Tinkerforge/thermal-imaging-bricklet/software/src/lepton.c

/* thermal-imaging-bricklet
 * Copyright (C) 2017 Olaf Lüke <olaf@tinkerforge.com>
 *
 * lepton.c: Lepton thermal imaging camera module communication
 *
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
 * You should have received a copy of the GNU Lesser General Public
 * License along with this library; if not, write to the
 * Free Software Foundation, Inc., 59 Temple Place - Suite 330,
 * Boston, MA 02111-1307, USA.
 */

#include "lepton.h"

#include <stdbool.h>

#include "configs/config.h"
#include "configs/config_lepton.h"

#include "bricklib2/hal/system_timer/system_timer.h"
#include "bricklib2/utility/crc16.h"

#include "communication.h"

#include "xmc_i2c.h"
#include "xmc_spi.h"
#include "xmc_gpio.h"
#include "xmc_usic.h"
#include "xmc_eru.h"

#define lepton_rx_read_irq_handler   IRQ_Hdlr_11
#define lepton_rx_remove_irq_handler IRQ_Hdlr_12
#define lepton_sync_handler          IRQ_Hdlr_3

extern Lepton lepton;

uint16_t * const lepton_frame_start = lepton.frame.buffer;
uint16_t * const lepton_frame_end = lepton.frame.buffer + LEPTON_FRAME_SIZE_WITH_TELEMETRY;
uint16_t * const lepton_frame_end_of_first_packet = lepton.frame.buffer + LEPTON_PACKET_SIZE;
uint16_t * const lepton_frame_last_full = lepton.frame.buffer + LEPTON_FRAME_SIZE_WITH_TELEMETRY-12;
uint16_t * const lepton_frame_first_packet_last_full = lepton.frame.buffer + LEPTON_PACKET_SIZE-2;
uint16_t *lepton_frame_pointer = lepton.frame.buffer;
uint16_t *lepton_frame_pointer_dummy = lepton.frame.buffer;

#if 0
uint16_t * const lepton_packet_start = lepton.packet.buffer;
uint16_t * const lepton_packet_end = lepton.packet.buffer + LEPTON_PACKET_SIZE;
uint16_t * const lepton_packet_last_full = lepton.packet.buffer + LEPTON_PACKET_SIZE-2;
uint16_t *lepton_packet_pointer = lepton.packet.buffer;
#endif

#define LEPTON_SET_SPI_LIMIT(limit) do {\
	LEPTON_SPI->RBCTR = (uint32_t)((LEPTON_SPI->RBCTR & (uint32_t)~USIC_CH_RBCTR_LIMIT_Msk) | ((limit) << USIC_CH_RBCTR_LIMIT_Pos));\
} while(0)

#define LEPTON_SPI_WRITE_1() do {\
	LEPTON_SPI_IN_PTR[0] = 0;\
} while(0)


#define LEPTON_SPI_WRITE_2() do {\
	LEPTON_SPI_WRITE_1();\
	LEPTON_SPI_WRITE_1();\
} while(0)

#define LEPTON_SPI_WRITE_4() do {\
	LEPTON_SPI_WRITE_2();\
	LEPTON_SPI_WRITE_2();\
} while(0)

#define LEPTON_SPI_WRITE_6() do {\
	LEPTON_SPI_WRITE_4();\
	LEPTON_SPI_WRITE_2();\
} while(0)

#define LEPTON_SPI_WRITE_8() do {\
	LEPTON_SPI_WRITE_6();\
	LEPTON_SPI_WRITE_2();\
} while(0)

#define LEPTON_SPI_WRITE_10() do {\
	LEPTON_SPI_WRITE_8();\
	LEPTON_SPI_WRITE_2();\
} while(0)

#define LEPTON_SPI_WRITE_12() do {\
	LEPTON_SPI_WRITE_10();\
	LEPTON_SPI_WRITE_2();\
} while(0)

#define LEPTON_SPI_WRITE_14() do {\
	LEPTON_SPI_WRITE_12();\
	LEPTON_SPI_WRITE_2();\
} while(0)

#define LEPTON_SPI_WRITE_16() do {\
	LEPTON_SPI_WRITE_14();\
	LEPTON_SPI_WRITE_2();\
} while(0)

#define LEPTON_SPI_READ_1() do {\
	*lepton_frame_pointer++ = *LEPTON_SPI_OUTR_PTR;\
} while(0)

#define LEPTON_SPI_READ_2() do {\
	LEPTON_SPI_READ_1();\
	LEPTON_SPI_READ_1();\
} while(0)

#define LEPTON_SPI_READ_4() do {\
	LEPTON_SPI_READ_2();\
	LEPTON_SPI_READ_2();\
} while(0)

#define LEPTON_SPI_READ_6() do {\
	LEPTON_SPI_READ_4();\
	LEPTON_SPI_READ_2();\
} while(0)

#define LEPTON_SPI_READ_8() do {\
	LEPTON_SPI_READ_6();\
	LEPTON_SPI_READ_2();\
} while(0)

#define LEPTON_SPI_READ_10() do {\
	LEPTON_SPI_READ_8();\
	LEPTON_SPI_READ_2();\
} while(0)

#define LEPTON_SPI_READ_12() do {\
	LEPTON_SPI_READ_10();\
	LEPTON_SPI_READ_2();\
} while(0)

#define LEPTON_SPI_READ_14() do {\
	LEPTON_SPI_READ_12();\
	LEPTON_SPI_READ_2();\
} while(0)

#define LEPTON_SPI_READ_16() do {\
	LEPTON_SPI_READ_14();\
	LEPTON_SPI_READ_2();\
} while(0)

#define LEPTON_SPI_REMOVE_1() do {\
	*LEPTON_SPI_OUTR_PTR;\
	lepton_frame_pointer_dummy++;\
} while(0)

#define LEPTON_SPI_REMOVE_2() do {\
	LEPTON_SPI_REMOVE_1();\
	LEPTON_SPI_REMOVE_1();\
} while(0)

#define LEPTON_SPI_REMOVE_4() do {\
	LEPTON_SPI_REMOVE_2();\
	LEPTON_SPI_REMOVE_2();\
} while(0)

#define LEPTON_SPI_REMOVE_6() do {\
	LEPTON_SPI_REMOVE_4();\
	LEPTON_SPI_REMOVE_2();\
} while(0)

#define LEPTON_SPI_REMOVE_8() do {\
	LEPTON_SPI_REMOVE_6();\
	LEPTON_SPI_REMOVE_2();\
} while(0)

#define LEPTON_SPI_REMOVE_10() do {\
	LEPTON_SPI_REMOVE_8();\
	LEPTON_SPI_REMOVE_2();\
} while(0)

#define LEPTON_SPI_REMOVE_12() do {\
	LEPTON_SPI_REMOVE_10();\
	LEPTON_SPI_REMOVE_2();\
} while(0)

#define LEPTON_SPI_REMOVE_14() do {\
	LEPTON_SPI_REMOVE_12();\
	LEPTON_SPI_REMOVE_2();\
} while(0)

#define LEPTON_SPI_REMOVE_16() do {\
	LEPTON_SPI_REMOVE_14();\
	LEPTON_SPI_REMOVE_2();\
} while(0)

typedef enum {
	LEPTON_IRQ_STATE_SYNC,
	LEPTON_IRQ_STATE_DATA
} LeptonIRQState;

static LeptonIRQState lepton_irq_state = LEPTON_IRQ_STATE_SYNC;

void __attribute__((optimize("-O3"))) lepton_sync_handler(void) {
	if(!lepton.sync_done || lepton.active_interface != LEPTON_INTERFACE_SPI || !XMC_GPIO_GetInput(LEPTON_SELECT_PIN)) {
		return;
	}

	// Use local pointer to save the time for accessing the struct
	volatile const uint32_t *LEPTON_SPI_OUTR_PTR = &LEPTON_SPI->OUTR;
	volatile uint32_t       *LEPTON_SPI_IN_PTR   =  LEPTON_SPI->IN;

	// Make sure SPI FIFO is flushed
	for(uint8_t i = 0; i < 32; i++) {
		*LEPTON_SPI_OUTR_PTR;
	}

	if(lepton.state == LEPTON_STATE_READ_FRAME) {
		XMC_USIC_CH_RXFIFO_SetInterruptNodePointer(LEPTON_SPI, XMC_USIC_CH_RXFIFO_INTERRUPT_NODE_POINTER_STANDARD, LEPTON_SERVICE_REQUEST_READ_RX);   // IRQ LEPTON_IRQ_READ_RX
		NVIC_DisableIRQ((IRQn_Type)LEPTON_IRQ_REMOVE_RX);
		NVIC_EnableIRQ((IRQn_Type)LEPTON_IRQ_READ_RX);
		lepton_frame_pointer = lepton_frame_start;
	} else {
		XMC_USIC_CH_RXFIFO_SetInterruptNodePointer(LEPTON_SPI, XMC_USIC_CH_RXFIFO_INTERRUPT_NODE_POINTER_STANDARD, LEPTON_SERVICE_REQUEST_REMOVE_RX); // IRQ LEPTON_IRQ_REMOVE_RX
		NVIC_DisableIRQ((IRQn_Type)LEPTON_IRQ_READ_RX);
		NVIC_EnableIRQ((IRQn_Type)LEPTON_IRQ_REMOVE_RX);
		lepton_frame_pointer_dummy = lepton_frame_start;
	}
	XMC_GPIO_SetOutputLow(LEPTON_SELECT_PIN);

	LEPTON_SET_SPI_LIMIT(15);
	lepton_irq_state = LEPTON_IRQ_STATE_SYNC;
	LEPTON_SPI_WRITE_16();
}

void __attribute__((optimize("-O3"))) __attribute__ ((section (".ram_code"))) lepton_rx_read_irq_handler(void) {
	// Use local pointer to save the time for accessing the struct
	volatile const uint32_t *LEPTON_SPI_OUTR_PTR = &LEPTON_SPI->OUTR;
	volatile uint32_t       *LEPTON_SPI_IN_PTR   =  LEPTON_SPI->IN;

	if(lepton_irq_state == LEPTON_IRQ_STATE_SYNC) {
		LEPTON_SPI_READ_2();
		if(lepton_frame_pointer != lepton_frame_end_of_first_packet) {
			LEPTON_SPI_READ_14();
			LEPTON_SPI_WRITE_2();
			if(lepton_frame_pointer != lepton_frame_first_packet_last_full) {
				LEPTON_SPI_WRITE_14();
			} else {
				LEPTON_SET_SPI_LIMIT(1);
			}
		} else {
			if((lepton.frame.data.packets[0].vospi.id & LEPTON_SPI_PACKET_ID_MASK) != 0) {
				lepton_frame_pointer = lepton_frame_start;
			} else {
				lepton_irq_state = LEPTON_IRQ_STATE_DATA;
			}
			LEPTON_SET_SPI_LIMIT(15);
			LEPTON_SPI_WRITE_16();
		}
	} else {
		LEPTON_SPI_READ_12();
		if(lepton_frame_pointer != lepton_frame_end) {
			// Write 10 words already before we read the next 4, we can save some waiting time between packets with this.
			// We don't write the full 12 bytes, we may get an early interrupt if we do.
			LEPTON_SPI_WRITE_10();
			LEPTON_SPI_READ_4();
			LEPTON_SPI_WRITE_2();
			if(lepton_frame_pointer != lepton_frame_last_full) {
				LEPTON_SPI_WRITE_4();
			} else {
				LEPTON_SET_SPI_LIMIT(11);
			}
		} else {
			lepton.state = LEPTON_STATE_CHECK_CRC;
			lepton.config_handle_now = true;
			XMC_GPIO_SetOutputHigh(LEPTON_SELECT_PIN);
		}
	}
}

void __attribute__((optimize("-O3"))) __attribute__ ((section (".ram_code"))) lepton_rx_remove_irq_handler(void) {
	// Use local pointer to save the time for accessing the struct
	volatile const uint32_t *LEPTON_SPI_OUTR_PTR = &LEPTON_SPI->OUTR;
	volatile uint32_t       *LEPTON_SPI_IN_PTR   =  LEPTON_SPI->IN;

	if(lepton_irq_state == LEPTON_IRQ_STATE_SYNC) {
		LEPTON_SPI_REMOVE_2();
		if(lepton_frame_pointer_dummy != lepton_frame_end_of_first_packet) {
			LEPTON_SPI_REMOVE_14();
			LEPTON_SPI_WRITE_2();
			if(lepton_frame_pointer_dummy != lepton_frame_first_packet_last_full) {
				LEPTON_SPI_WRITE_14();
			} else {
				LEPTON_SET_SPI_LIMIT(1);
			}
		} else {
			if((lepton.frame.data.packets[0].vospi.id & LEPTON_SPI_PACKET_ID_MASK) != 0) {
				lepton_frame_pointer_dummy = lepton_frame_start;
			} else {
				lepton_irq_state = LEPTON_IRQ_STATE_DATA;
			}
			LEPTON_SET_SPI_LIMIT(15);
			LEPTON_SPI_WRITE_16();
		}
	} else {
		LEPTON_SPI_REMOVE_12();
		if(lepton_frame_pointer_dummy != lepton_frame_end) {
			// Write 10 words already before we read the next 4, we can save some waiting time between packets with this.
			// We don't write the full 12 bytes, we may get an early interrupt if we do.
			LEPTON_SPI_WRITE_10();
			LEPTON_SPI_REMOVE_4();
			LEPTON_SPI_WRITE_2();
			if(lepton_frame_pointer_dummy != lepton_frame_last_full) {
				LEPTON_SPI_WRITE_4();
			} else {
				LEPTON_SET_SPI_LIMIT(11);
			}
		} else {
			XMC_GPIO_SetOutputHigh(LEPTON_SELECT_PIN);
			lepton.config_handle_now = true;
		}
	}
}

void lepton_i2c_write(Lepton *lepton, const uint16_t reg, const uint16_t length, const uint16_t *data, bool send_stop) {
	// Send address
	XMC_I2C_CH_MasterStart(LEPTON_I2C, LEPTON_I2C_ADDRESS << 1, XMC_I2C_CH_CMD_WRITE);

	// Wait for ACK
	while(!(XMC_I2C_CH_GetStatusFlag(LEPTON_I2C) & XMC_I2C_CH_STATUS_FLAG_ACK_RECEIVED));
	XMC_I2C_CH_ClearStatusFlag(LEPTON_I2C, XMC_I2C_CH_STATUS_FLAG_ACK_RECEIVED);

	// Transmit 16 bit register
	XMC_I2C_CH_MasterTransmit(LEPTON_I2C, reg >> 8);
	XMC_I2C_CH_MasterTransmit(LEPTON_I2C, reg & 0xFF);

	// Transmit data
	uint32_t index = 0;
	bool high = true;
	while(index < length) {
		while(!XMC_USIC_CH_TXFIFO_IsFull(LEPTON_I2C)) {
			if(index < length) {
				if(high) {
					// Send high byte first
					XMC_I2C_CH_MasterTransmit(LEPTON_I2C, data[index] >> 8);
					high = false;
				} else {
					// and low byte second
					XMC_I2C_CH_MasterTransmit(LEPTON_I2C, data[index] & 0xFF);
					high = true;
					index++;
				}
			} else {
				break;
			}
		}
	}

	// Wait for data to be written
	while(!XMC_USIC_CH_TXFIFO_IsEmpty(LEPTON_I2C));

	if(send_stop) {
		// Send stop
		XMC_I2C_CH_MasterStop(LEPTON_I2C);
	}
}

void lepton_i2c_read(Lepton *lepton, const uint16_t reg, const uint32_t length, uint16_t *data) {
	// Write register address to read from without stop bit
	lepton_i2c_write(lepton, reg, 0, NULL, false);

	// Repeated start
	XMC_I2C_CH_MasterRepeatedStart(LEPTON_I2C, LEPTON_I2C_ADDRESS << 1, XMC_I2C_CH_CMD_READ);

	// Wait for ACK
	while(!(XMC_I2C_CH_GetStatusFlag(LEPTON_I2C) & XMC_I2C_CH_STATUS_FLAG_ACK_RECEIVED));
	XMC_I2C_CH_ClearStatusFlag(LEPTON_I2C, XMC_I2C_CH_STATUS_FLAG_ACK_RECEIVED);

	uint32_t fifo_index = 0;
	uint32_t data_index = 0;
	bool high = true;
	while(fifo_index < length*2) {
		while(!XMC_USIC_CH_TXFIFO_IsFull(LEPTON_I2C)) {
			if(fifo_index < length*2) {
				if(fifo_index+1 == length*2) {
					XMC_I2C_CH_MasterReceiveNack(LEPTON_I2C);
				} else {
					XMC_I2C_CH_MasterReceiveAck(LEPTON_I2C);
				}
				fifo_index++;
			} else {
				break;
			}
		}

		while(data_index < fifo_index) {
			while(XMC_USIC_CH_RXFIFO_IsEmpty(LEPTON_I2C));
			if(high) {
				// Get high byte first
				data[data_index/2] = XMC_I2C_CH_GetReceivedData(LEPTON_I2C) << 8;
				high = false;
			} else {
				// and low byte second
				data[data_index/2] |= XMC_I2C_CH_GetReceivedData(LEPTON_I2C);
				high = true;
			}
			data_index++;
		}
	}
	XMC_I2C_CH_MasterStop(LEPTON_I2C);
}

void lepton_spi_select(Lepton *lepton) {
	XMC_GPIO_SetOutputLow(LEPTON_SELECT_PIN);
}

void lepton_spi_deselect(Lepton *lepton) {
	XMC_GPIO_SetOutputHigh(LEPTON_SELECT_PIN);
}

uint16_t lepton_get_status(Lepton *lepton) {
	uint16_t status = 0;
	lepton_i2c_read(lepton, LEPTON_I2C_STATUS_REG, 1, &status);
	return status;
}

bool lepton_is_busy(Lepton *lepton) {
	uint16_t status = lepton_get_status(lepton);
	return status & LEPTON_I2C_STATUS_BUSY_BITMASK;
}

void lepton_command_run(Lepton *lepton, const uint16_t command_id) {
	while(lepton_is_busy(lepton));

	// Write command
	uint16_t command = command_id | LEPTON_I2C_COMMAND_TYPE_RUN;
	lepton_i2c_write(lepton, LEPTON_I2C_COMMAND_REG, 1, &command, true);

	while(lepton_is_busy(lepton));
}

void lepton_attribute_read(Lepton *lepton, const uint16_t command_id, const uint16_t length, uint16_t *data) {
	while(lepton_is_busy(lepton));

	// Write length to be read
	lepton_i2c_write(lepton, LEPTON_I2C_DATA_LENGTH_REG, 1, &length, true);

	// Write command
	uint16_t command = command_id | LEPTON_I2C_COMMAND_TYPE_GET;
	lepton_i2c_write(lepton, LEPTON_I2C_COMMAND_REG, 1, &command, true);

	while(lepton_is_busy(lepton));

	// Read data
	lepton_i2c_read(lepton, LEPTON_I2C_DATA_0_REG, length, data);
}

void lepton_attribute_write(Lepton *lepton, const uint16_t command_id, const uint16_t length, uint16_t *data) {
	while(lepton_is_busy(lepton));

	// Write data (we assume length <= 16 here)
	lepton_i2c_write(lepton, LEPTON_I2C_DATA_0_REG, length, data, true);

	// Write length
	lepton_i2c_write(lepton, LEPTON_I2C_DATA_LENGTH_REG, 1, &length, true);

	// Write command
	uint16_t command = command_id | LEPTON_I2C_COMMAND_TYPE_SET;
	lepton_i2c_write(lepton, LEPTON_I2C_COMMAND_REG, 1, &command, true);

	while(lepton_is_busy(lepton));
}

void lepton_reset(Lepton *lepton) {
	XMC_GPIO_SetOutputLow(LEPTON_NRESET_PIN);
	lepton->reset_start_time = system_timer_get_ms();
	lepton->state = LEPTON_STATE_RESET;
}

void lepton_init_spi(Lepton *lepton) {
	if(lepton->active_interface == LEPTON_INTERFACE_SPI) {
		return;
	}

	// -- First disable I2C --
	XMC_I2C_CH_Stop(LEPTON_I2C);

	const XMC_GPIO_CONFIG_t sda_pin_config =  {
		.mode         = XMC_GPIO_MODE_INPUT_TRISTATE,
		.output_level = XMC_GPIO_OUTPUT_LEVEL_HIGH,
	};

	const XMC_GPIO_CONFIG_t scl_pin_config = {
		.mode         = XMC_GPIO_MODE_INPUT_TRISTATE,
		.output_level = XMC_GPIO_OUTPUT_LEVEL_HIGH,
	};

	XMC_GPIO_Init(LEPTON_SDA_PIN, &sda_pin_config);
	XMC_GPIO_Init(LEPTON_SCL_PIN, &scl_pin_config);


	// -- Then enable SPI --

	// USIC channel configuration
	const XMC_SPI_CH_CONFIG_t channel_config = {
		.baudrate       = LEPTON_SPI_BAUDRATE,
		.bus_mode       = XMC_SPI_CH_BUS_MODE_MASTER,
		.selo_inversion = XMC_SPI_CH_SLAVE_SEL_INV_TO_MSLS,
		.parity_mode    = XMC_USIC_CH_PARITY_MODE_NONE
	};

	// MISO pin configuration
	const XMC_GPIO_CONFIG_t miso_pin_config = {
		.mode             = XMC_GPIO_MODE_INPUT_TRISTATE,
		.input_hysteresis = XMC_GPIO_INPUT_HYSTERESIS_LARGE
	};

	// SCLK pin configuration
	const XMC_GPIO_CONFIG_t sclk_pin_config = {
		.mode             = LEPTON_SCLK_PIN_AF,
		.output_level     = XMC_GPIO_OUTPUT_LEVEL_HIGH
	};

	// SELECT pin configuration
	const XMC_GPIO_CONFIG_t select_pin_config = {
		.mode             = XMC_GPIO_MODE_OUTPUT_PUSH_PULL, // we set cs high/low by hand
		.output_level     = XMC_GPIO_OUTPUT_LEVEL_HIGH
	};

	// Configure MISO pin
	XMC_GPIO_Init(LEPTON_MISO_PIN, &miso_pin_config);

	// Initialize USIC channel in SPI master mode
	XMC_SPI_CH_Init(LEPTON_SPI, &channel_config);
	LEPTON_SPI->SCTR &= ~USIC_CH_SCTR_PDL_Msk; // Set passive data level to 0
	LEPTON_SPI->PCR_SSCMode &= ~USIC_CH_PCR_SSCMode_TIWEN_Msk; // Disable time between bytes

	XMC_SPI_CH_SetBitOrderMsbFirst(LEPTON_SPI);

	XMC_SPI_CH_SetWordLength(LEPTON_SPI, 16);
	XMC_SPI_CH_SetFrameLength(LEPTON_SPI, 64);

	XMC_SPI_CH_SetTransmitMode(LEPTON_SPI, XMC_SPI_CH_MODE_STANDARD);

	// Configure the clock polarity and clock delay
	XMC_SPI_CH_ConfigureShiftClockOutput(LEPTON_SPI,
									     XMC_SPI_CH_BRG_SHIFT_CLOCK_PASSIVE_LEVEL_1_DELAY_DISABLED,
									     XMC_SPI_CH_BRG_SHIFT_CLOCK_OUTPUT_SCLK);
	// Configure Leading/Trailing delay
	XMC_SPI_CH_SetSlaveSelectDelay(LEPTON_SPI, 2);

	// Set input source path
	XMC_SPI_CH_SetInputSource(LEPTON_SPI, LEPTON_MISO_INPUT, LEPTON_MISO_SOURCE);

	// SPI Mode: CPOL=1 and CPHA=1
	LEPTON_SPI_CHANNEL->DX1CR |= USIC_CH_DX1CR_DPOL_Msk;

	XMC_USIC_CH_TXFIFO_Flush(LEPTON_SPI);
	XMC_USIC_CH_RXFIFO_Flush(LEPTON_SPI);

	// Configure transmit FIFO
	XMC_USIC_CH_TXFIFO_Configure(LEPTON_SPI, 48, XMC_USIC_CH_FIFO_SIZE_16WORDS, 0);

	// Configure receive FIFO
	XMC_USIC_CH_RXFIFO_Configure(LEPTON_SPI, 32, XMC_USIC_CH_FIFO_SIZE_16WORDS, 15);

	// Set priority and enable NVIC node for receive interrupt
	NVIC_SetPriority((IRQn_Type)LEPTON_IRQ_READ_RX, LEPTON_IRQ_RX_PRIORITY);
	NVIC_SetPriority((IRQn_Type)LEPTON_IRQ_REMOVE_RX, LEPTON_IRQ_RX_PRIORITY);

	// Start SPI
	XMC_SPI_CH_Start(LEPTON_SPI);

	// Configure SCLK pin
	XMC_GPIO_Init(LEPTON_SCLK_PIN, &sclk_pin_config);

	// Configure slave select pin
	XMC_GPIO_Init(LEPTON_SELECT_PIN, &select_pin_config);

	XMC_USIC_CH_RXFIFO_EnableEvent(LEPTON_SPI, XMC_USIC_CH_RXFIFO_EVENT_CONF_STANDARD | XMC_USIC_CH_RXFIFO_EVENT_CONF_ALTERNATE);

	lepton->active_interface = LEPTON_INTERFACE_SPI;
}

void lepton_init_i2c(Lepton *lepton) {
	if(lepton->active_interface == LEPTON_INTERFACE_I2C) {
		return;
	}

	// -- First disable SPI --

	XMC_SPI_CH_Stop(LEPTON_SPI);
	lepton_spi_deselect(lepton);

	NVIC_DisableIRQ((IRQn_Type)LEPTON_IRQ_REMOVE_RX);
	NVIC_DisableIRQ((IRQn_Type)LEPTON_IRQ_READ_RX);

	XMC_USIC_CH_RXFIFO_DisableEvent(LEPTON_SPI, XMC_USIC_CH_RXFIFO_EVENT_CONF_STANDARD | XMC_USIC_CH_RXFIFO_EVENT_CONF_ALTERNATE);

	// MISO pin configuration
	const XMC_GPIO_CONFIG_t miso_pin_config = {
		.mode             = XMC_GPIO_MODE_INPUT_TRISTATE,
		.input_hysteresis = XMC_GPIO_INPUT_HYSTERESIS_LARGE
	};

	// SCLK pin configuration
	const XMC_GPIO_CONFIG_t sclk_pin_config = {
		.mode             = XMC_GPIO_MODE_OUTPUT_PUSH_PULL,
		.output_level     = XMC_GPIO_OUTPUT_LEVEL_HIGH
	};

	// SELECT pin configuration
	const XMC_GPIO_CONFIG_t select_pin_config = {
		.mode             = XMC_GPIO_MODE_OUTPUT_PUSH_PULL,
		.output_level     = XMC_GPIO_OUTPUT_LEVEL_HIGH
	};

	XMC_GPIO_Init(LEPTON_SCLK_PIN, &sclk_pin_config);
	XMC_GPIO_Init(LEPTON_MISO_PIN, &miso_pin_config);
	XMC_GPIO_Init(LEPTON_SELECT_PIN, &select_pin_config);

	LEPTON_SPI->SCTR |= USIC_CH_SCTR_PDL_Msk; // Set passive data level to 1
	LEPTON_SPI_CHANNEL->DX1CR &= ~USIC_CH_DX1CR_DPOL_Msk; // Set input control register back to default


	// -- Then enable I2C --

	const XMC_I2C_CH_CONFIG_t master_channel_config = {
		.baudrate = LEPTON_I2C_BAUDRATE,
		.address  = 0
	};

	const XMC_GPIO_CONFIG_t sda_pin_config =  {
		.mode         = LEPTON_SDA_PIN_MODE,
		.output_level = XMC_GPIO_OUTPUT_LEVEL_HIGH,
	};

	const XMC_GPIO_CONFIG_t scl_pin_config = {
		.mode         = LEPTON_SCL_PIN_MODE,
		.output_level = XMC_GPIO_OUTPUT_LEVEL_HIGH,
	};

	XMC_I2C_CH_Init(LEPTON_I2C, &master_channel_config);

	XMC_USIC_CH_SetInputSource(LEPTON_I2C, LEPTON_SDA_INPUT, LEPTON_SDA_SOURCE);
	XMC_USIC_CH_SetInputSource(LEPTON_I2C, LEPTON_SCL_INPUT, LEPTON_SCL_SOURCE);

	XMC_USIC_CH_TXFIFO_Flush(LEPTON_I2C);
	XMC_USIC_CH_RXFIFO_Flush(LEPTON_I2C);

	XMC_USIC_CH_TXFIFO_Configure(LEPTON_I2C, 48, XMC_USIC_CH_FIFO_SIZE_16WORDS, 0);
	XMC_USIC_CH_RXFIFO_Configure(LEPTON_I2C, 32, XMC_USIC_CH_FIFO_SIZE_16WORDS, 0);

	XMC_I2C_CH_Start(LEPTON_I2C);

	XMC_GPIO_Init(LEPTON_SDA_PIN, &sda_pin_config);
	XMC_GPIO_Init(LEPTON_SCL_PIN, &scl_pin_config);

	lepton->active_interface = LEPTON_INTERFACE_I2C;
}

void lepton_init_gpio(Lepton *lepton) {
	const XMC_GPIO_CONFIG_t nreset_pin_config = {
		.mode         = XMC_GPIO_MODE_OUTPUT_PUSH_PULL,
		.output_level = XMC_GPIO_OUTPUT_LEVEL_LOW,
	};
	XMC_GPIO_Init(LEPTON_NRESET_PIN, &nreset_pin_config);

	const XMC_GPIO_CONFIG_t sync_pin_config = {
		.mode             = XMC_GPIO_MODE_INPUT_TRISTATE,
		.input_hysteresis = XMC_GPIO_INPUT_HYSTERESIS_LARGE
	};
	XMC_GPIO_Init(P0_0, &sync_pin_config); // TODO: Remove me for release version

	const XMC_ERU_ETL_CONFIG_t sync_etl_config = {
		.input_a                = (uint32_t)XMC_ERU_ETL_INPUT_A0,
		.input_b                = (uint32_t)XMC_ERU_ETL_INPUT_B0,
		.enable_output_trigger  = (uint32_t)1,
		.edge_detection         = XMC_ERU_ETL_EDGE_DETECTION_RISING,
		.output_trigger_channel = XMC_ERU_ETL_OUTPUT_TRIGGER_CHANNEL0, // Select the source for event
		.source                 = XMC_ERU_ETL_SOURCE_B
	};

	// Initializes input pin characteristics
	XMC_GPIO_Init(LEPTON_SYNC_PIN, &sync_pin_config);
	// ERU Event Trigger Logic Hardware initialization based on UI
	XMC_ERU_ETL_Init(XMC_ERU0, LEPTON_SYNC_ETL_CHANNEL, &sync_etl_config);
	// OGU is configured to generate event on configured trigger edge
	XMC_ERU_OGU_SetServiceRequestMode(XMC_ERU0, LEPTON_SYNC_OGU_CHANNEL, XMC_ERU_OGU_SERVICE_REQUEST_ON_TRIGGER);
	// Configure NVIC node and priority
	NVIC_SetPriority(LEPTON_SYNC_IRQ_N, LEPTON_SYNC_IRQ_PRIO);

	// Clear pending interrupt before enabling it
	NVIC_ClearPendingIRQ(LEPTON_SYNC_IRQ_N);
	// Enable NVIC node
	NVIC_EnableIRQ(LEPTON_SYNC_IRQ_N);
}

void lepton_init(Lepton *lepton) {
	memset(lepton, 0, sizeof(Lepton));
	lepton->active_interface = LEPTON_INTERFACE_NONE;

	lepton->agc.region_of_interest[0] = 0;
	lepton->agc.region_of_interest[1] = 0;
	lepton->agc.region_of_interest[2] = 79;
	lepton->agc.region_of_interest[3] = 59;
	lepton->agc.dampening_factor      = 64;
	lepton->agc.clip_limit[0]         = 4800;
	lepton->agc.clip_limit[1]         = 512;
	lepton->agc.empty_counts          = 2;
	lepton->spotmeter_roi[0]          = 39;
	lepton->spotmeter_roi[1]          = 29;
	lepton->spotmeter_roi[2]          = 40;
	lepton->spotmeter_roi[3]          = 30;
	lepton->resolution                = 1;
	lepton->current_callback_config   = THERMAL_IMAGING_IMAGE_TRANSFER_MANUAL_HIGH_CONTRAST_IMAGE;
	lepton->flux_linear_parameters.scene_emissivity       = 8192;
	lepton->flux_linear_parameters.temperature_background = 29515;
	lepton->flux_linear_parameters.tau_window             = 8192;
	lepton->flux_linear_parameters.temperatur_window      = 29515;
	lepton->flux_linear_parameters.tau_atmosphere         = 8192;
	lepton->flux_linear_parameters.temperature_atmosphere = 29515;
	lepton->flux_linear_parameters.reflection_window      = 0;
	lepton->flux_linear_parameters.temperature_reflection = 29515;
	lepton->sys_ffc_shutter_mode.shutter_mode                = 1;
	lepton->sys_ffc_shutter_mode.temp_lockout_state          = 0;
	lepton->sys_ffc_shutter_mode.video_freeze_during_ffc     = 1;
	lepton->sys_ffc_shutter_mode.ffc_desired                 = 0;
	lepton->sys_ffc_shutter_mode.elapsed_time_since_last_ffc = 0;
	lepton->sys_ffc_shutter_mode.desired_ffc_period          = 300000;
	lepton->sys_ffc_shutter_mode.explicit_cmd_to_open        = 0;
	lepton->sys_ffc_shutter_mode.desired_ffc_temp_delta      = 300;
	lepton->sys_ffc_shutter_mode.imminent_delay              = 52;

	lepton_init_gpio(lepton);
	lepton_init_i2c(lepton);
	lepton_reset(lepton);
}

bool lepton_check_crc_of_first_packet(Lepton *lepton) {
	// First sanity check the id.
	if(((lepton->frame.data.packets[0].vospi.id & LEPTON_SPI_DISCARD_PACKET_ID_MASK) != LEPTON_SPI_DISCARD_PACKET_ID_MASK) &&
	   ((lepton->frame.data.packets[0].vospi.id & 0x00FF) > LEPTON_FRAME_ROWS)) {
		return false;
	}

	// Remove first 4 bits of id, set crc to 0 in packet to calculate CRC
	// See p52ff in datasheet.
	lepton->frame.data.packets[0].vospi.id &= LEPTON_SPI_PACKET_ID_MASK;
	const uint16_t crc_lepton = lepton->frame.data.packets[0].vospi.crc;
	lepton->frame.data.packets[0].vospi.crc = 0;

	return crc_lepton == crc16_ccitt_16in(lepton->frame.data.packets[0].buffer, LEPTON_PACKET_SIZE);
}

void lepton_handle_reset(Lepton *lepton) {
	// To reset the Lepton we assert the reset line for LEPTON_RESET_TIME ms
	if(lepton->reset_start_time != 0) {
		if(system_timer_is_time_elapsed_ms(lepton->reset_start_time, LEPTON_RESET_TIME)) {
			lepton->reset_start_time = 0;

			XMC_GPIO_SetOutputHigh(LEPTON_NRESET_PIN);
			lepton->boot_start_time = system_timer_get_ms();
		}

		return;
	}

	// Make sure that we only talk to the Lepton after the specified bootup time
	if(lepton->boot_start_time != 0) {
		if(system_timer_is_time_elapsed_ms(lepton->boot_start_time, LEPTON_BOOTUP_TIME)) {
			const uint16_t status = lepton_get_status(lepton);
			// Check if camera really has bootet
			if(status & LEPTON_I2C_STATUS_BOOT_STATUS_BITMASK) {
				lepton->boot_start_time = 0;
				lepton->state = LEPTON_STATE_INIT;
			}
		}
	}
}

void lepton_handle_init(Lepton *lepton) {
	uint32_t enable = 1;
	lepton_attribute_write(lepton, LEPTON_CID_AGC_CALC_ENABLE_STATE, 2, (uint16_t*)&enable);
	lepton_attribute_write(lepton, LEPTON_CID_AGC_ENABLE_STATE, 2, (uint16_t*)&enable);

	uint32_t telemetry_location = 1; // footer
	lepton_attribute_write(lepton, LEPTON_CID_SYS_TELEMETRY_LOCATION, 2, (uint16_t*)&telemetry_location);

	uint32_t telemetry_enable = 1;
	lepton_attribute_write(lepton, LEPTON_CID_SYS_TELEMETRY_ENABLE_STATE, 2, (uint16_t*)&telemetry_enable);

	uint32_t oem_status = 1;
	while(oem_status != 0) {
		lepton_attribute_read(lepton, LEPTON_CID_OEM_STATUS, 2, (uint16_t*)&oem_status);
	}
	uint32_t gpio_mode = 5; // vsync
	lepton_attribute_write(lepton, LEPTON_CID_OEM_GPIO_MODE_SELECT, 2, (uint16_t*)&gpio_mode);
	while(oem_status != 0) {
		lepton_attribute_read(lepton, LEPTON_CID_OEM_STATUS, 2, (uint16_t*)&oem_status);
	}

	uint32_t rad_status = 1;
	while(rad_status != 0) {
		lepton_attribute_read(lepton, LEPTON_CID_RAD_RUN_STATUS, 2, (uint16_t*)&rad_status);
	}
	uint32_t tlinear_enable = 0;
	lepton_attribute_write(lepton, LEPTON_CID_RAD_TLINEAR_ENABLE_STATE, 2, (uint16_t*)&tlinear_enable);
	while(rad_status != 0) {
		lepton_attribute_read(lepton, LEPTON_CID_RAD_RUN_STATUS, 2, (uint16_t*)&rad_status);
	}
	lepton->state = LEPTON_STATE_SYNC;
}

void lepton_handle_sync(Lepton *lepton) {
	if(lepton->sync_start_time == 0) {
		lepton->sync_done = false;
		lepton_init_spi(lepton);
		lepton->packet_next_id = 0;
		lepton->image_buffer_receive_index = 0;
		lepton->image_buffer_stream_index = 0;

		lepton->sync_start_time = system_timer_get_ms();

		lepton_spi_select(lepton);

	}

	if(system_timer_is_time_elapsed_ms(lepton->sync_start_time, 190)) {
		lepton->sync_start_time = 0;
		lepton->state = LEPTON_STATE_READ_FRAME;
		lepton->sync_done = true;
		lepton_spi_deselect(lepton);
	}
}

void lepton_handle_configuration(Lepton *lepton) {
	if(lepton->config_handle_now) {
		lepton->config_handle_now = false;
		if(lepton->config_bitmask) {
			lepton_init_i2c(lepton);

			if(lepton->config_bitmask & LEPTON_CONFIG_BITMASK_AGC_ENABLE) {
				uint32_t enabled = 1; // Enable tlinear in temperature mode
				if((lepton->current_callback_config == THERMAL_IMAGING_IMAGE_TRANSFER_CALLBACK_HIGH_CONTRAST_IMAGE) ||
				   (lepton->current_callback_config == THERMAL_IMAGING_IMAGE_TRANSFER_MANUAL_HIGH_CONTRAST_IMAGE)) {
					enabled = 0; // Disable tlinear in high contrast mode
				}

				uint32_t rad_status = 1;
				while(rad_status != 0) {
					lepton_attribute_read(lepton, LEPTON_CID_RAD_RUN_STATUS, 2, (uint16_t*)&rad_status);
				}
				lepton_attribute_write(lepton, LEPTON_CID_RAD_TLINEAR_ENABLE_STATE, 2, (uint16_t*)&enabled);
				while(rad_status != 0) {
					lepton_attribute_read(lepton, LEPTON_CID_RAD_RUN_STATUS, 2, (uint16_t*)&rad_status);
				}

				if(enabled) {
					enabled = 0; // Disable agc in temperature mode
				} else {
					enabled = 1; // Enable agc in high contrast mode
				}

				lepton_attribute_write(lepton, LEPTON_CID_AGC_ENABLE_STATE, 2, (uint16_t*)&enabled);
				lepton->config_bitmask &= ~LEPTON_CONFIG_BITMASK_AGC_ENABLE;

			} else if(lepton->config_bitmask & LEPTON_CONFIG_BITMASK_AGC_ROI) {
				uint16_t roi[4] = {lepton->agc.region_of_interest[0], lepton->agc.region_of_interest[1], lepton->agc.region_of_interest[2], lepton->agc.region_of_interest[3]};
				lepton_attribute_write(lepton, LEPTON_CID_AGC_ROI, 4, roi);
				lepton->config_bitmask &= ~LEPTON_CONFIG_BITMASK_AGC_ROI;

			} else if(lepton->config_bitmask & LEPTON_CONFIG_BITMASK_AGC_DAMPENING_FACTOR) {
				lepton_attribute_write(lepton, LEPTON_CID_AGC_HEQ_DAMPENING_FACTOR, 1, &lepton->agc.dampening_factor);
				lepton->config_bitmask &= ~LEPTON_CONFIG_BITMASK_AGC_DAMPENING_FACTOR;

			} else if(lepton->config_bitmask & LEPTON_CONFIG_BITMASK_AGC_CLIP_LIMIT) {
				lepton_attribute_write(lepton, LEPTON_CID_AGC_HEQ_CLIP_LIMIT_HIGH, 1, &lepton->agc.clip_limit[0]);
				lepton_attribute_write(lepton, LEPTON_CID_AGC_HEQ_CLIP_LIMIT_LOW,  1, &lepton->agc.clip_limit[1]);
				lepton->config_bitmask &= ~LEPTON_CONFIG_BITMASK_AGC_CLIP_LIMIT;

			} else if(lepton->config_bitmask & LEPTON_CONFIG_BITMASK_AGC_EMPTY_COUNTS) {
				lepton_attribute_write(lepton, LEPTON_CID_AGC_HEQ_EMPTY_COUNTS, 1, &lepton->agc.empty_counts);
				lepton->config_bitmask &= ~LEPTON_CONFIG_BITMASK_AGC_EMPTY_COUNTS;
			} else if(lepton->config_bitmask & LEPTON_CONFIG_BITMASK_SPOTMETER_ROI) {
				uint32_t rad_status = 1;
				while(rad_status != 0) {
					lepton_attribute_read(lepton, LEPTON_CID_RAD_RUN_STATUS, 2, (uint16_t*)&rad_status);
				}
				uint16_t roi[4] = {lepton->spotmeter_roi[1], lepton->spotmeter_roi[0], lepton->spotmeter_roi[3], lepton->spotmeter_roi[2]};
				lepton_attribute_write(lepton, LEPTON_CID_RAD_SPOTMETER_ROI, 4, roi);
				while(rad_status != 0) {
					lepton_attribute_read(lepton, LEPTON_CID_RAD_RUN_STATUS, 2, (uint16_t*)&rad_status);
				}
				lepton->config_bitmask &= ~LEPTON_CONFIG_BITMASK_SPOTMETER_ROI;
			} else if(lepton->config_bitmask & LEPTON_CONFIG_BITMASK_RESOLUTION) {
				uint32_t rad_status = 1;
				while(rad_status != 0) {
					lepton_attribute_read(lepton, LEPTON_CID_RAD_RUN_STATUS, 2, (uint16_t*)&rad_status);
				}
				uint32_t resolution = lepton->resolution;
				uint32_t gain_mode = 0; // 0 = high gain
				if(resolution == 0) { // res 0 = 0-6553 kelvin
					gain_mode = 1; // 1 = low gain (for hotter scenes)
				}
				lepton_attribute_write(lepton, LEPTON_CID_RAD_TLINEAR_RESOLUTION, 2, (uint16_t*)&resolution);
				rad_status = 1;
				while(rad_status != 0) {
					lepton_attribute_read(lepton, LEPTON_CID_RAD_RUN_STATUS, 2, (uint16_t*)&rad_status);
				}
				lepton_attribute_write(lepton, LEPTON_CID_SYS_GAIN_MODE, 2, (uint16_t*)&gain_mode);
				while(rad_status != 0) {
					lepton_attribute_read(lepton, LEPTON_CID_RAD_RUN_STATUS, 2, (uint16_t*)&rad_status);
				}
				lepton->config_bitmask &= ~LEPTON_CONFIG_BITMASK_RESOLUTION;
			} else if(lepton->config_bitmask & LEPTON_CONFIG_BITMASK_FLUX_PARAMETERS) {
				uint32_t rad_status = 1;
				while(rad_status != 0) {
					lepton_attribute_read(lepton, LEPTON_CID_RAD_RUN_STATUS, 2, (uint16_t*)&rad_status);
				}
				lepton_attribute_write(lepton, LEPTON_CID_RAD_FLUX_LINEAR_PARAMETERS, 8, (uint16_t*)&lepton->flux_linear_parameters);
				while(rad_status != 0) {
					lepton_attribute_read(lepton, LEPTON_CID_RAD_RUN_STATUS, 2, (uint16_t*)&rad_status);
				}

				lepton->config_bitmask &= ~LEPTON_CONFIG_BITMASK_FLUX_PARAMETERS;
			} else if(lepton->config_bitmask & LEPTON_CONFIG_BITMASK_SHUTTER_MODE) {
				uint32_t rad_status = 1;
				while(rad_status != 0) {
					lepton_attribute_read(lepton, LEPTON_CID_RAD_RUN_STATUS, 2, (uint16_t*)&rad_status);
				}
				lepton_attribute_write(lepton, LEPTON_CID_SYS_FFC_SHUTTER_MODE, 16, (uint16_t*)&lepton->sys_ffc_shutter_mode);
				while(rad_status != 0) {
					lepton_attribute_read(lepton, LEPTON_CID_RAD_RUN_STATUS, 2, (uint16_t*)&rad_status);
				}

				lepton->config_bitmask &= ~LEPTON_CONFIG_BITMASK_SHUTTER_MODE;
			} else if(lepton->config_bitmask & LEPTON_CONFIG_BITMASK_RUN_FFC) {
				uint32_t rad_status = 1;
				while(rad_status != 0) {
					lepton_attribute_read(lepton, LEPTON_CID_RAD_RUN_STATUS, 2, (uint16_t*)&rad_status);
				}
				lepton_command_run(&lepton, LEPTON_CID_SYS_RUN_FFC);
				while(rad_status != 0) {
					lepton_attribute_read(lepton, LEPTON_CID_RAD_RUN_STATUS, 2, (uint16_t*)&rad_status);
				}

				lepton->config_bitmask &= ~LEPTON_CONFIG_BITMASK_RUN_FFC;
			}

			lepton_init_spi(lepton);
		}
	}
}

void lepton_new_statistics(Lepton *lepton) {
	// Double buffer staticists, so there can't be any tearing
	// in the statistics data.
	lepton->statistics.spotmeter_statistics[0] = lepton->frame.data.telemetry.data.spotmeter_mean;
	lepton->statistics.spotmeter_statistics[1] = lepton->frame.data.telemetry.data.spotmeter_maximum;
	lepton->statistics.spotmeter_statistics[2] = lepton->frame.data.telemetry.data.spotmeter_minimum;
	lepton->statistics.spotmeter_statistics[3] = lepton->frame.data.telemetry.data.spotmeter_population;

	lepton->statistics.temperatures[0]         = lepton->frame.data.telemetry.data.fpa_temperature_kelvin;
	lepton->statistics.temperatures[1]         = lepton->frame.data.telemetry.data.fpa_temperature_at_last_ffc_kelvin;
	lepton->statistics.temperatures[2]         = lepton->frame.data.telemetry.data.housing_temperature_kelvin;
	lepton->statistics.temperatures[3]         = lepton->frame.data.telemetry.data.housing_temperature_at_last_ffc;

	lepton->statistics.resolution              = lepton->frame.data.telemetry.data.tlinear_resolution;

	const uint32_t status                      = lepton->frame.data.telemetry.data.status;
	lepton->statistics.ffc_status              = (status >> 4) & 0b11;
	lepton->statistics.temperature_warning     = (((status >> 15) & 1) << 0) | (((status >> 20) & 1) << 1);
}

void lepton_handle_crc(Lepton *lepton) {
	if(lepton_check_crc_of_first_packet(lepton)) {
		lepton_new_statistics(lepton);
		lepton->state = LEPTON_STATE_WRITE_FRAME;
	} else if(lepton->manual_transfer_ongoing) {
		lepton->state = LEPTON_STATE_WRITE_FRAME;
	} else {
		lepton->state = LEPTON_STATE_READ_FRAME;
	}
}

void lepton_tick(Lepton *lepton) {
	switch(lepton->state) {
		case LEPTON_STATE_RESET: lepton_handle_reset(lepton); break;
		case LEPTON_STATE_INIT: lepton_handle_init(lepton); break;
		case LEPTON_STATE_SYNC:  lepton_handle_sync(lepton); break;
		case LEPTON_STATE_READ_FRAME:
		case LEPTON_STATE_WRITE_FRAME: lepton_handle_configuration(lepton); break;
		case LEPTON_STATE_CHECK_CRC: lepton_handle_crc(lepton); break;
	}
}

bool lepton_has_started(Lepton *lepton) {
	return (lepton->reset_start_time == 0) && (lepton->boot_start_time == 0);
}
